dongseon-jeong/low_cost_humanoid_demo/rasberrypi/catkin_ws/src/legs_description/meshes/ll6_1.stl

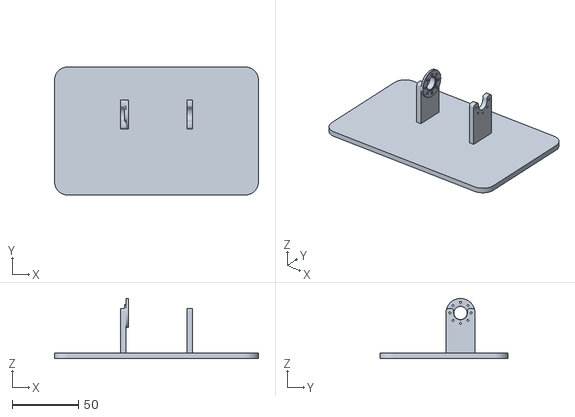
[picture p25: CAD file, 2026-05-30]
rasberrypi/catkin_ws/src/legs_description/meshes/ll6_1.stl
154.5 x 97.0 x 45.5
