dongseon-jeong/low_cost_humanoid_demo/train_arm/3d/arm/main_parts/x2/wrist_gear_drive.stl

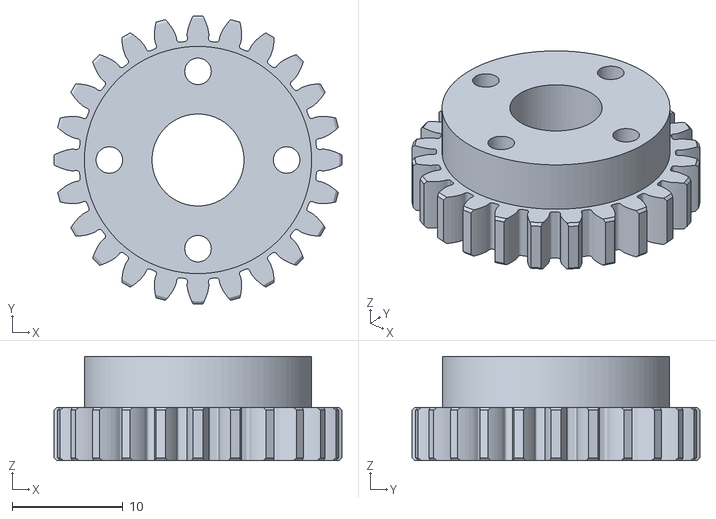
[picture p26: CAD file, 2026-06-26]
train_arm/3d/arm/main_parts/x2/wrist_gear_drive.stl
26.0 x 26.0 x 9.40
