dongseon-jeong/low_cost_humanoid_demo/train_arm/3d/arm/parts/bearing_684x4.stl

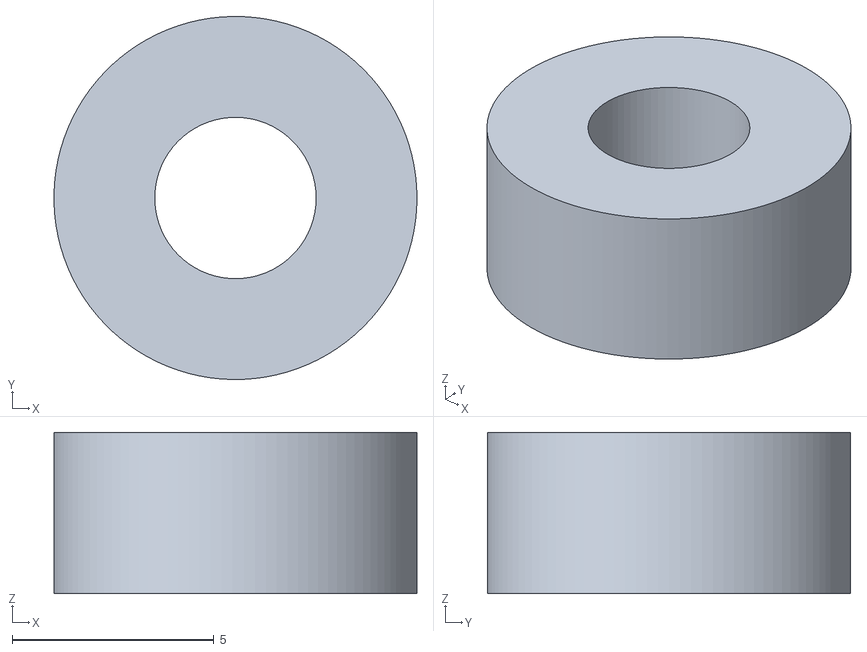
[picture p27: CAD file, 2026-06-26]
train_arm/3d/arm/parts/bearing_684x4.stl
9.00 x 9.00 x 4.00
