dongseon-jeong/low_cost_humanoid_demo/train_arm/3d/neck_pitch.stl

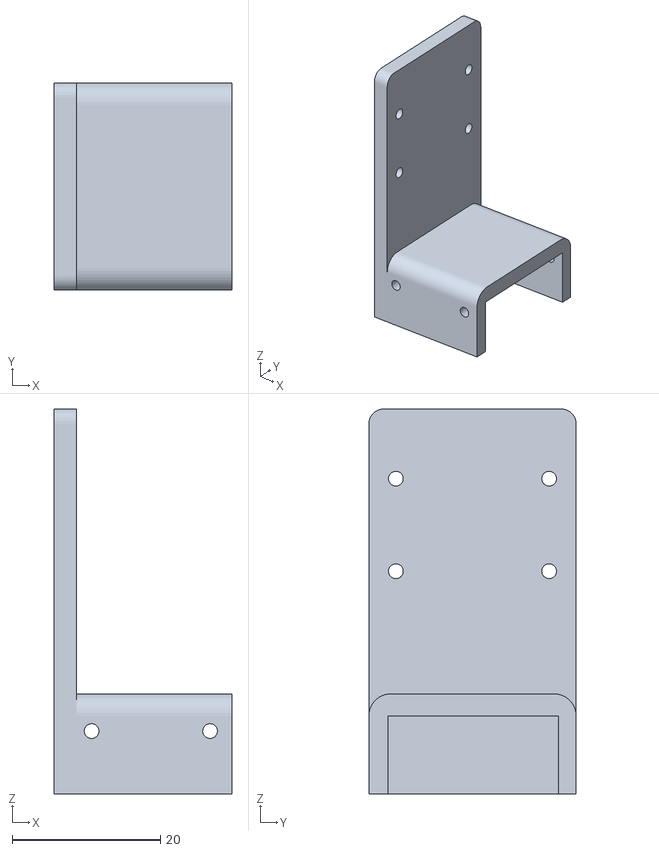
[picture p28: CAD file, 2026-06-26]
train_arm/3d/neck_pitch.stl
24.0 x 28.0 x 52.0
