dongseon-jeong/low_cost_humanoid_demo/train_leg/3d/leg/ll1.stl

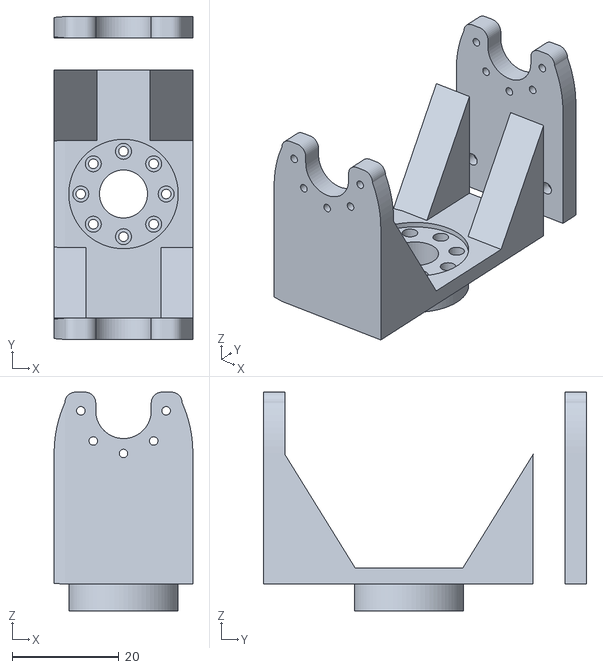
[picture p29: CAD file, 2026-05-30]
train_leg/3d/leg/ll1.stl
26.0 x 60.5 x 41.0
