dongseon-jeong/low_cost_humanoid_demo/rasberrypi/catkin_ws/src/humanoid_urdf_description/meshes/relbow_1.stl

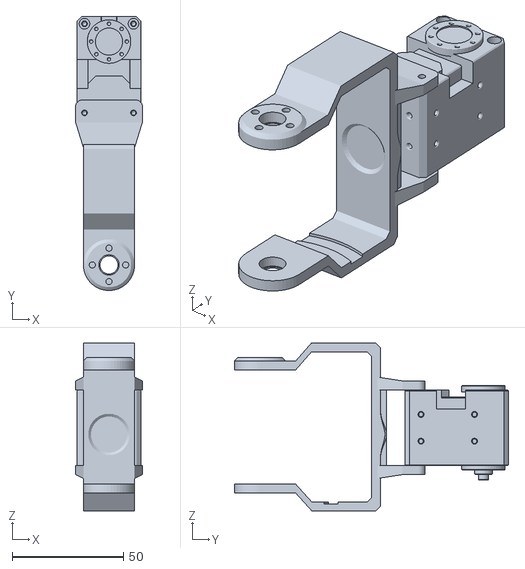
[picture p30: CAD file, 2026-06-21]
rasberrypi/catkin_ws/src/humanoid_urdf_description/meshes/relbow_1.stl
30.0 x 122.9 x 75.3
