dongseon-jeong/low_cost_humanoid_demo/rasberrypi/catkin_ws/src/legs_description/meshes/rl1_1.stl

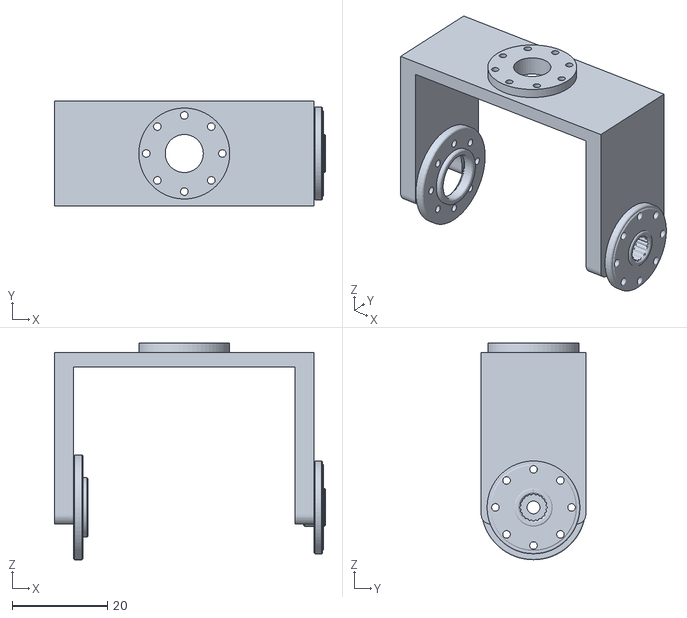
[picture p31: CAD file, 2026-05-30]
rasberrypi/catkin_ws/src/legs_description/meshes/rl1_1.stl
56.9 x 22.0 x 45.5
