dongseon-jeong/low_cost_humanoid_demo/train_arm/3d/330cap.stl

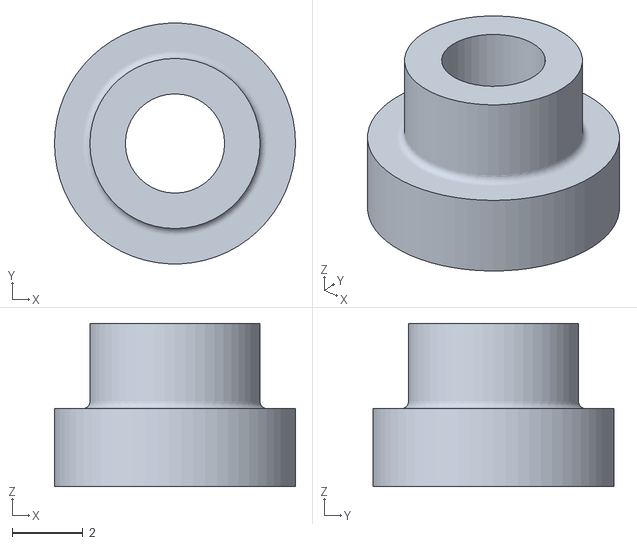
[picture p32: CAD file, 2026-06-26]
train_arm/3d/330cap.stl
6.80 x 6.79 x 4.60
