dongseon-jeong/low_cost_humanoid_demo/train_arm/3d/arm/main_parts/x2/gripper_gear_drive.stl

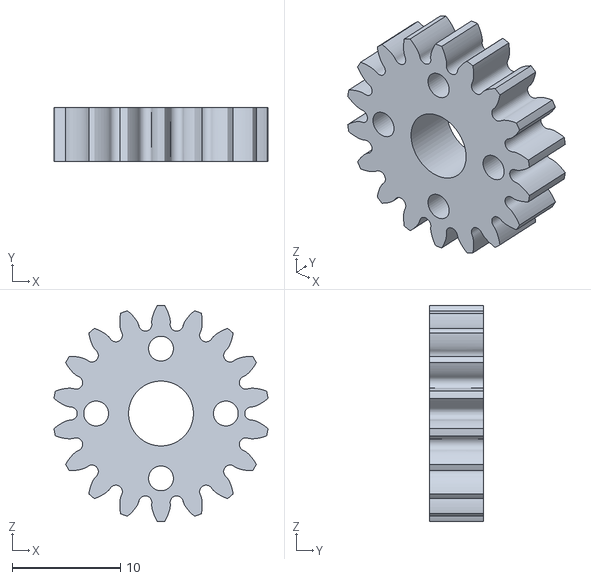
[picture p33: CAD file, 2026-06-26]
train_arm/3d/arm/main_parts/x2/gripper_gear_drive.stl
19.8 x 5.00 x 20.0
