dongseon-jeong/low_cost_humanoid_demo/train_arm/humanoid_urdf_description/meshes/rl4_1.stl

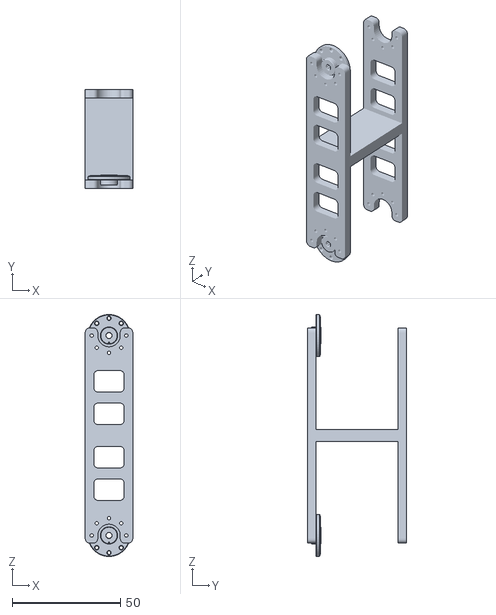
[picture p34: CAD file, 2026-06-21]
train_arm/humanoid_urdf_description/meshes/rl4_1.stl
22.0 x 46.0 x 112.0
