dongseon-jeong/low_cost_humanoid_demo/train_leg/3d/leg/body.stl

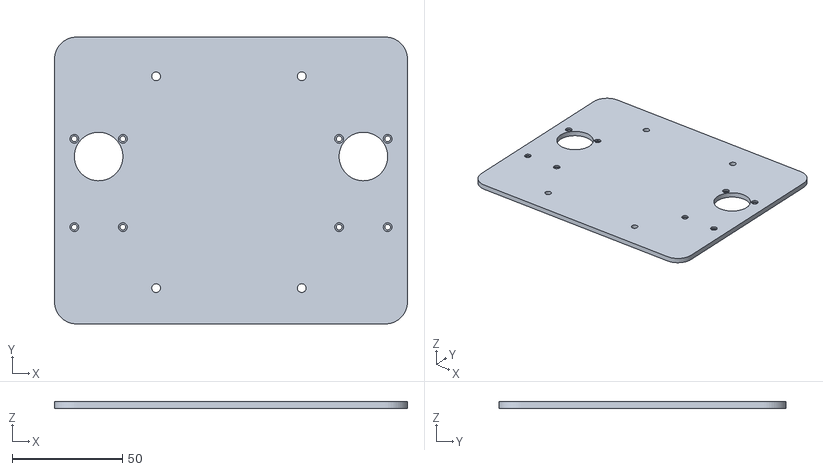
[picture p35: CAD file, 2026-05-30]
train_leg/3d/leg/body.stl
160.0 x 130.0 x 3.00
