dongseon-jeong/low_cost_humanoid_demo/rasberrypi/catkin_ws/src/legs_description/meshes/base_link.stl

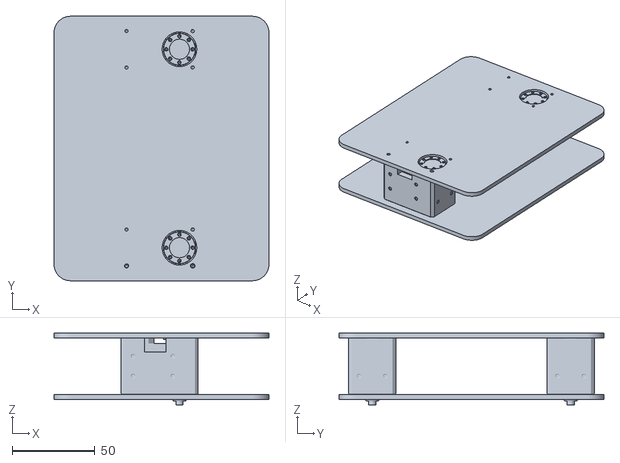
[picture p36: CAD file, 2026-05-30]
rasberrypi/catkin_ws/src/legs_description/meshes/base_link.stl
130.0 x 160.0 x 43.4
