dongseon-jeong/low_cost_humanoid_demo/train_arm/3d/arm/main_parts/x2/shoulder_yaw_link.stl

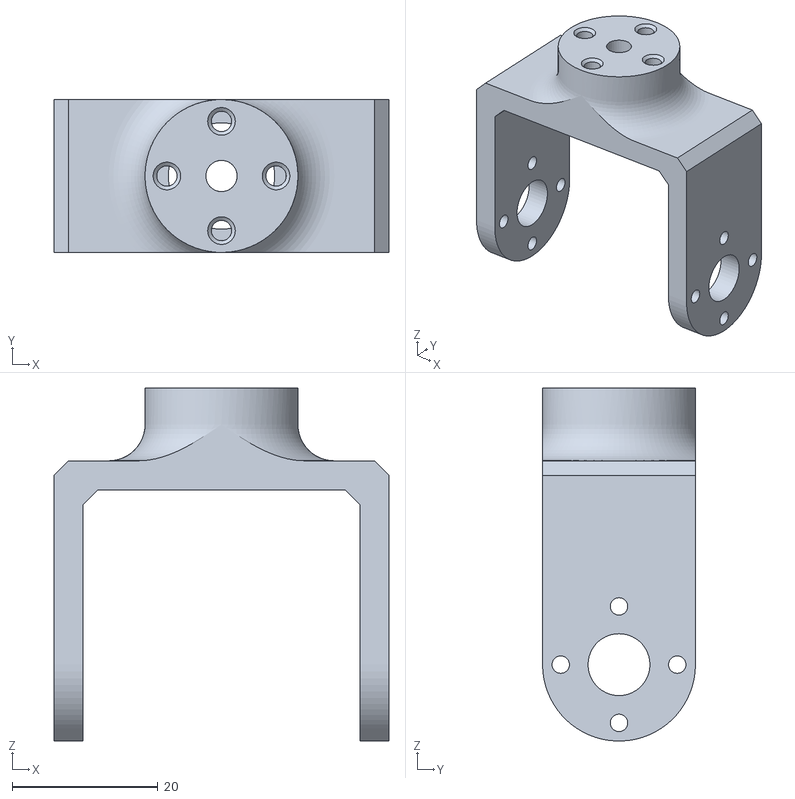
[picture p37: CAD file, 2026-06-26]
train_arm/3d/arm/main_parts/x2/shoulder_yaw_link.stl
46.0 x 21.0 x 48.5
