dongseon-jeong/low_cost_humanoid_demo/train_arm/3d/body2.stl

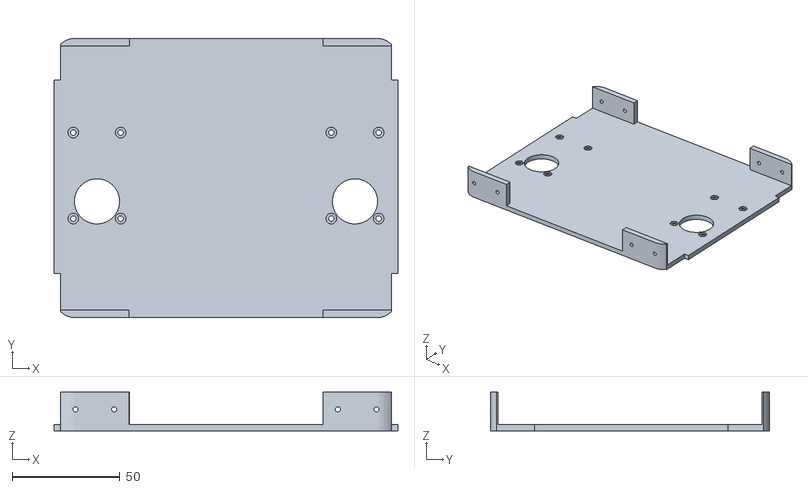
[picture p38: CAD file, 2026-06-26]
train_arm/3d/body2.stl
160.0 x 130.0 x 18.0
