dongseon-jeong/low_cost_humanoid_demo/train_leg/3d/leg/rl1.stl

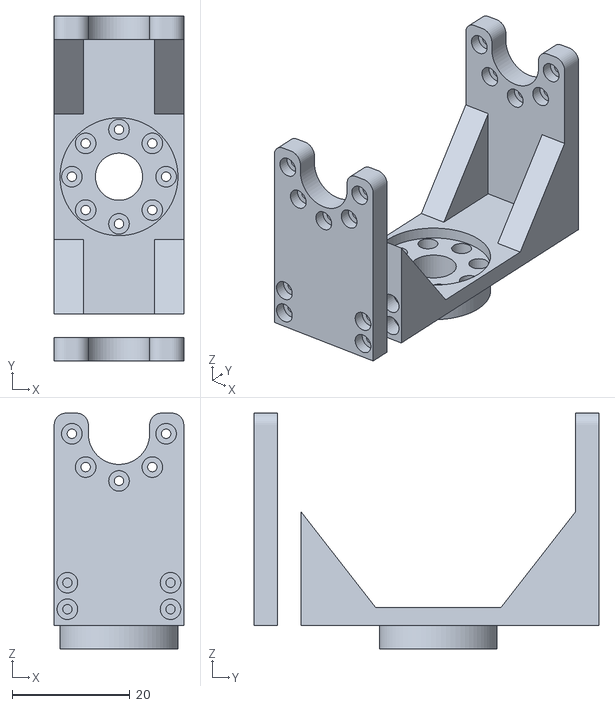
[picture p39: CAD file, 2026-05-30]
train_leg/3d/leg/rl1.stl
22.0 x 58.5 x 40.0
