dongseon-jeong/low_cost_humanoid_demo/train_arm/3d/arm/main_parts/x2/wrist_roll_link.stl

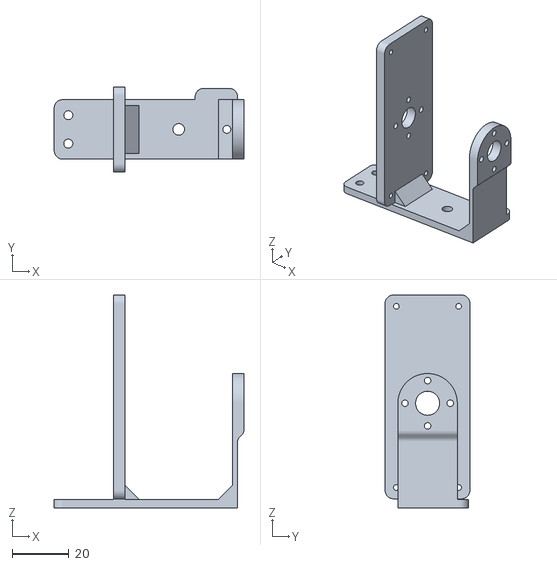
[picture p40: CAD file, 2026-06-26]
train_arm/3d/arm/main_parts/x2/wrist_roll_link.stl
67.0 x 30.0 x 75.2
