dongseon-jeong/low_cost_humanoid_demo/train_arm/3d/neck_roll.stl

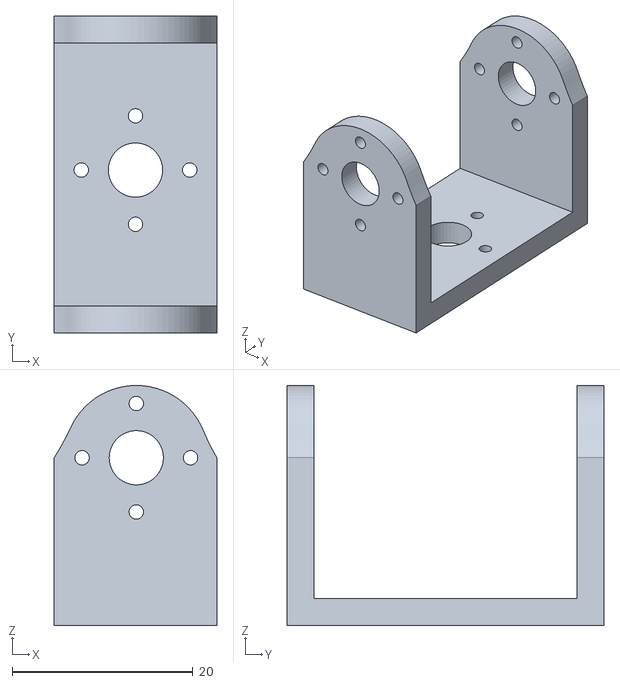
[picture p41: CAD file, 2026-06-26]
train_arm/3d/neck_roll.stl
18.0 x 35.1 x 26.6
