dongseon-jeong/low_cost_humanoid_demo/train_arm/humanoid_urdf_description/meshes/lshd_2xl_1.stl

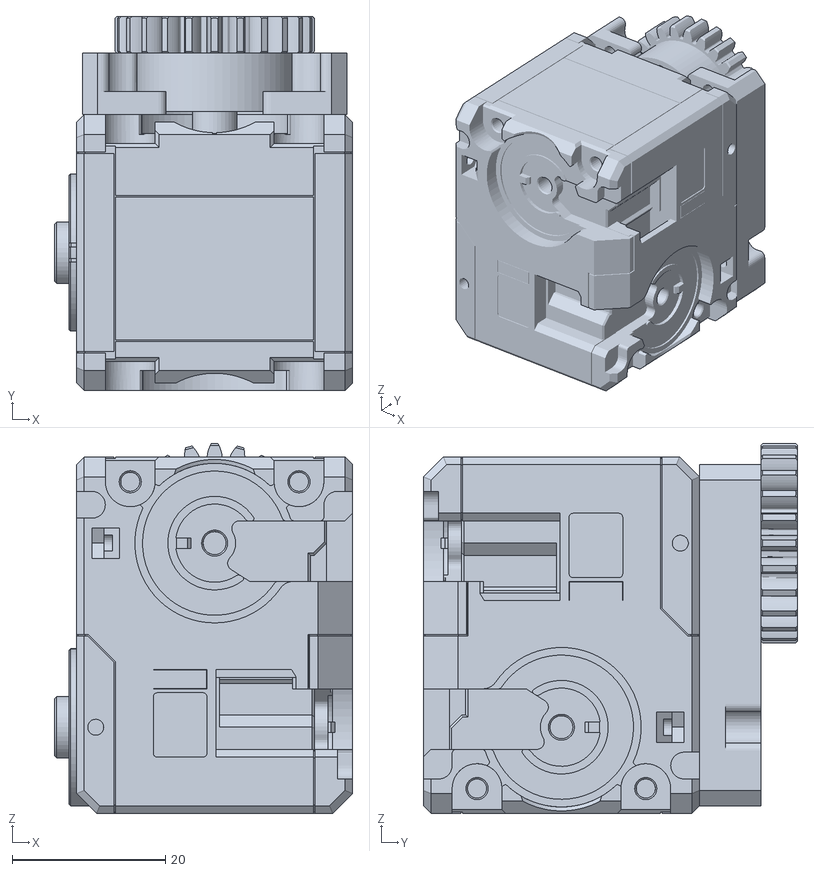
[picture p42: CAD file, 2026-06-21]
train_arm/humanoid_urdf_description/meshes/lshd_2xl_1.stl
38.9 x 48.8 x 48.2
