dongseon-jeong/low_cost_humanoid_demo/train_leg/3d/leg/rl4.stl

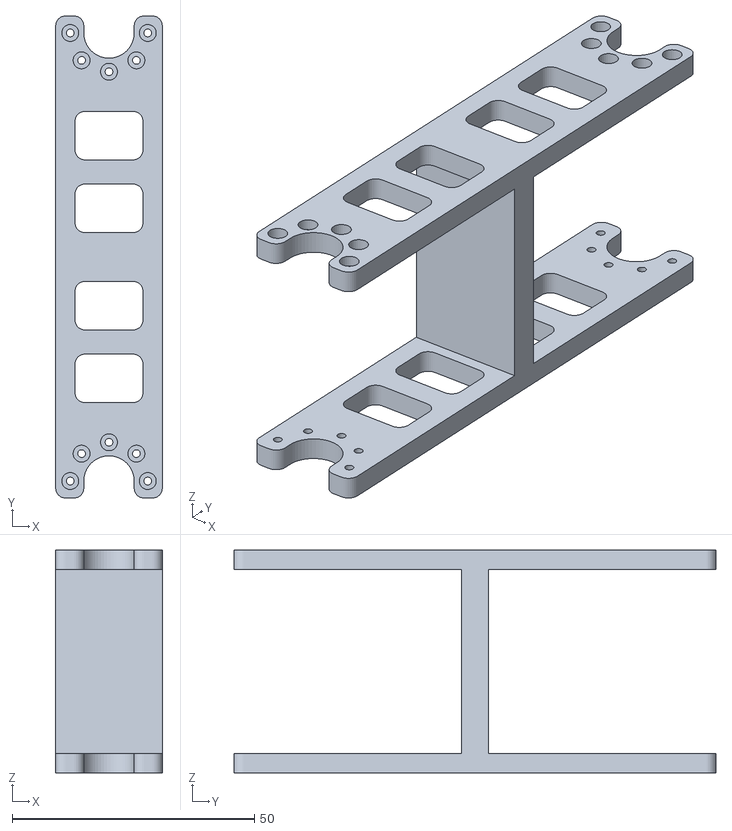
[picture p43: CAD file, 2026-04-02]
train_leg/3d/leg/rl4.stl
22.0 x 99.5 x 46.0
