dongseon-jeong/low_cost_humanoid_demo/rasberrypi/catkin_ws/src/humanoid_urdf_description/meshes/rl3_1.stl

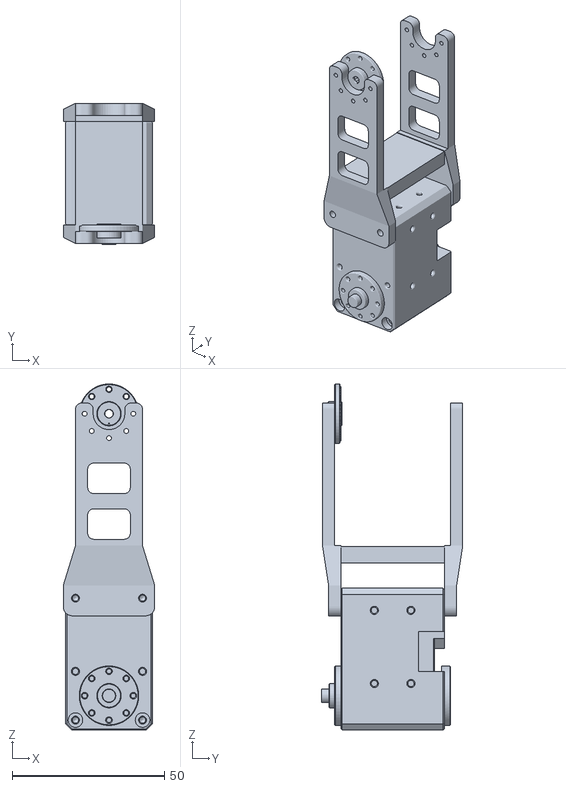
[picture p44: CAD file, 2026-06-21]
rasberrypi/catkin_ws/src/humanoid_urdf_description/meshes/rl3_1.stl
30.0 x 46.4 x 113.5
