dongseon-jeong/low_cost_humanoid_demo/train_arm/3d/arm/main_parts/x2/shoulder_gear_driven.stl

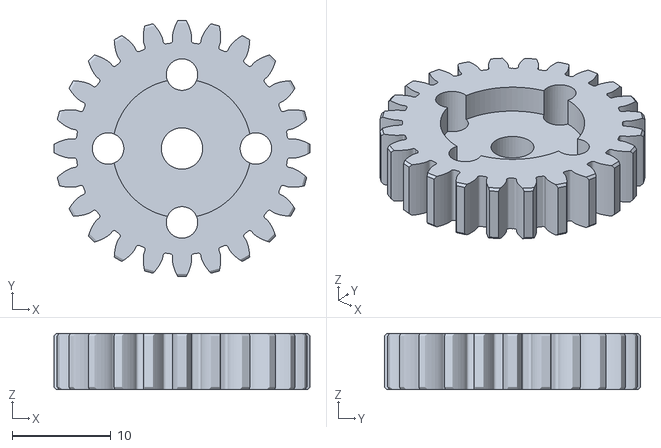
[picture p45: CAD file, 2026-06-26]
train_arm/3d/arm/main_parts/x2/shoulder_gear_driven.stl
26.0 x 26.0 x 5.70
