dongseon-jeong/low_cost_humanoid_demo/train_leg/3d/leg/rl3.stl

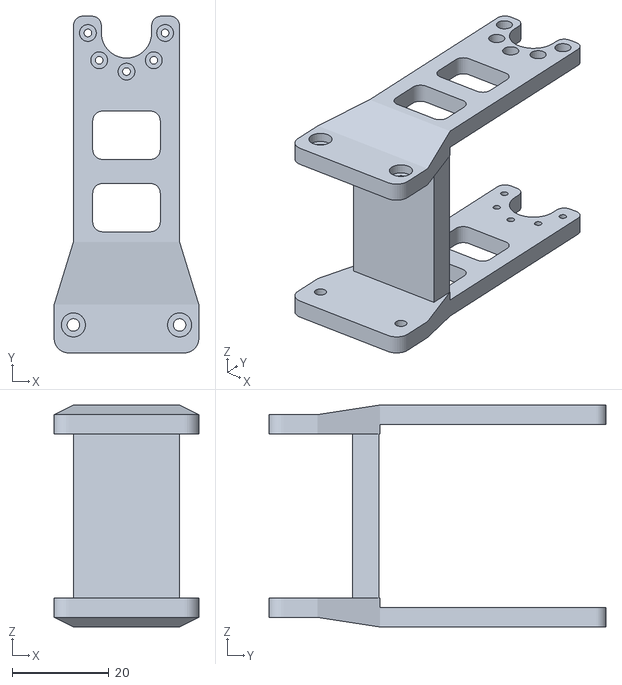
[picture p46: CAD file, 2026-04-02]
train_leg/3d/leg/rl3.stl
30.0 x 69.8 x 46.0
