dongseon-jeong/low_cost_humanoid_demo/train_leg/3d/leg/ll5.stl

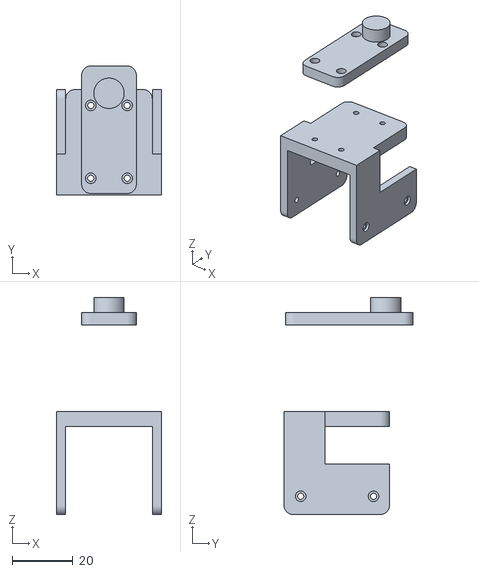
[picture p47: CAD file, 2026-04-02]
train_leg/3d/leg/ll5.stl
34.5 x 42.5 x 71.5
