dongseon-jeong/low_cost_humanoid_demo/train_arm/humanoid_urdf_description/meshes/rshd_2xl_1.stl

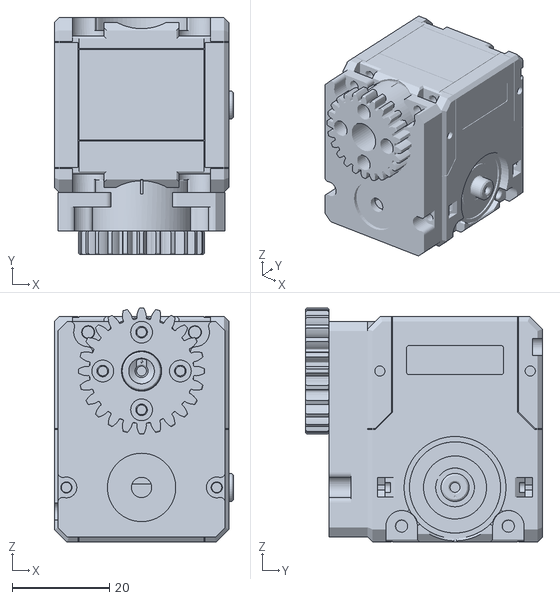
[picture p48: CAD file, 2026-06-21]
train_arm/humanoid_urdf_description/meshes/rshd_2xl_1.stl
37.0 x 48.8 x 48.2
