dongseon-jeong/low_cost_humanoid_demo/train_arm/3d/arm/main_parts/x2/offset_plate.stl

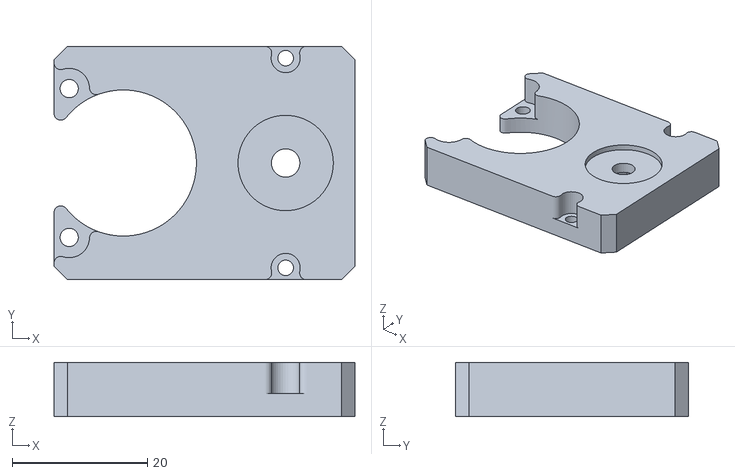
[picture p50: CAD file, 2026-06-26]
train_arm/3d/arm/main_parts/x2/offset_plate.stl
44.5 x 34.5 x 8.00
