dongseon-jeong/low_cost_humanoid_demo/train_arm/3d/arm/main_parts/x2/elbow_link_new.stl

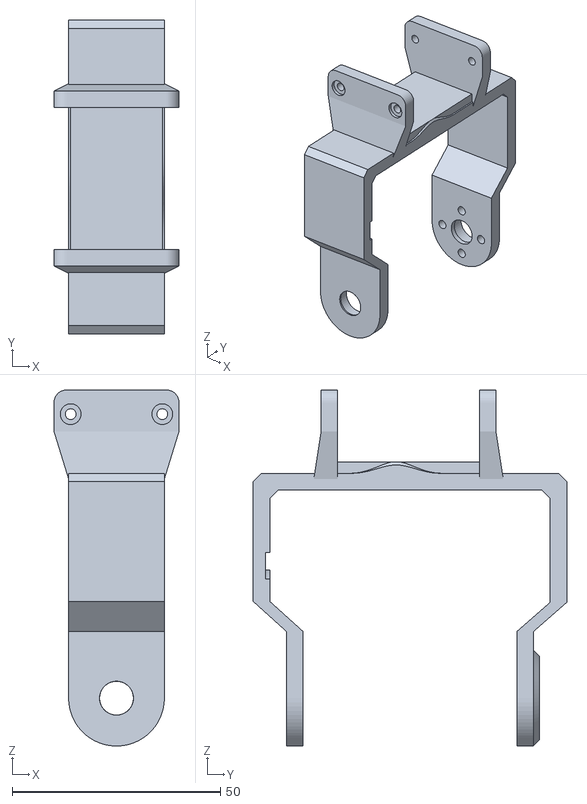
[picture p51: CAD file, 2026-06-26]
train_arm/3d/arm/main_parts/x2/elbow_link_new.stl
30.0 x 75.3 x 85.5
