dongseon-jeong/low_cost_humanoid_demo/rasberrypi/catkin_ws/src/humanoid_urdf_description/meshes/rwrist_1.stl

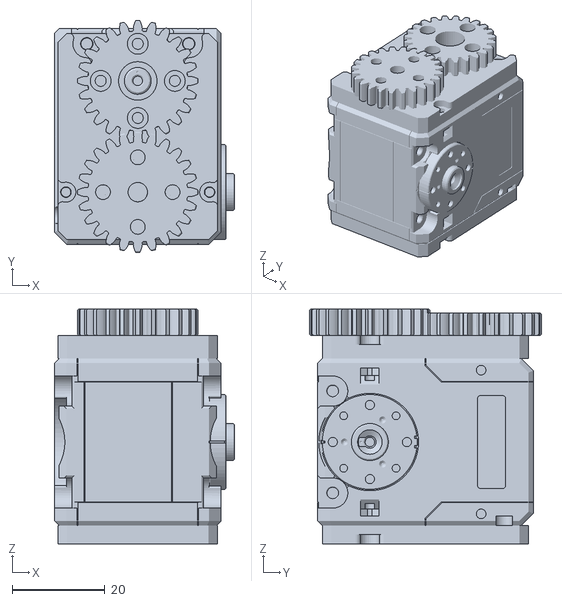
[picture p52: CAD file, 2026-06-21]
rasberrypi/catkin_ws/src/humanoid_urdf_description/meshes/rwrist_1.stl
38.9 x 50.0 x 50.7
