dongseon-jeong/low_cost_humanoid_demo/train_arm/humanoid_urdf_description/meshes/head_1.stl

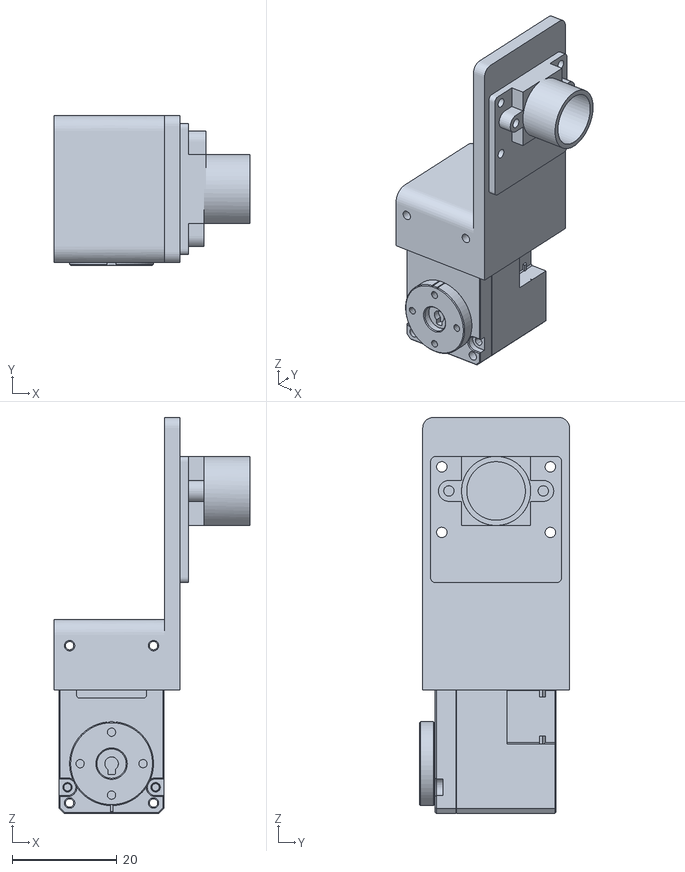
[picture p53: CAD file, 2026-06-21]
train_arm/humanoid_urdf_description/meshes/head_1.stl
37.3 x 28.6 x 75.5
